Makerfabs/ESP32-S3-4G-LTE-CAT1-A7670X/example/at_command_demo/at_command_demo.ino

#include <Arduino.h>

HardwareSerial mySerial2(2);

#define IO_RXD2 47
#define IO_TXD2 48

#define IO_GSM_PWRKEY 4
#define IO_GSM_RST    5

void setup() {
  // put your setup code here, to run once:
  Serial.begin(115200);
  Serial.print(F("Hello! ESP32-S3 AT command V1.0 Test"));
  mySerial2.begin(115200,SERIAL_8N1, IO_RXD2, IO_TXD2);
  pinMode(IO_GSM_RST, OUTPUT);
  digitalWrite(IO_GSM_RST, LOW);
  
  pinMode(IO_GSM_PWRKEY, OUTPUT);
  digitalWrite(IO_GSM_PWRKEY, HIGH);
  delay(3000);
  digitalWrite(IO_GSM_PWRKEY, LOW);

  int i = 10;
  Serial.println("\nTesting Module Response...\n");
  Serial.println("****");
  while (i) {
        mySerial2.println("AT");
        delay(500);
        if (mySerial2.available()) {
            String r = mySerial2.readString();
            Serial.println(r);
            if ( r.indexOf("OK") >= 0 ) {
                //reply = true;
                break;;
            }
            else
            {
              digitalWrite(IO_GSM_PWRKEY, HIGH);
              delay(3000);
              digitalWrite(IO_GSM_PWRKEY, LOW);
            }
        }
        delay(500);
        i--;
    }
    Serial.println("****\n");
}

void loop() {
  // put your main code here, to run repeatedly:
  while (Serial.available() > 0) {
    mySerial2.write(Serial.read());
    yield();
  }
  while (mySerial2.available() > 0) {
    Serial.write(mySerial2.read());
    yield();
  }
}
